ami3go/SLCAN-interface-hardware/Images/20240503_131544.jpg

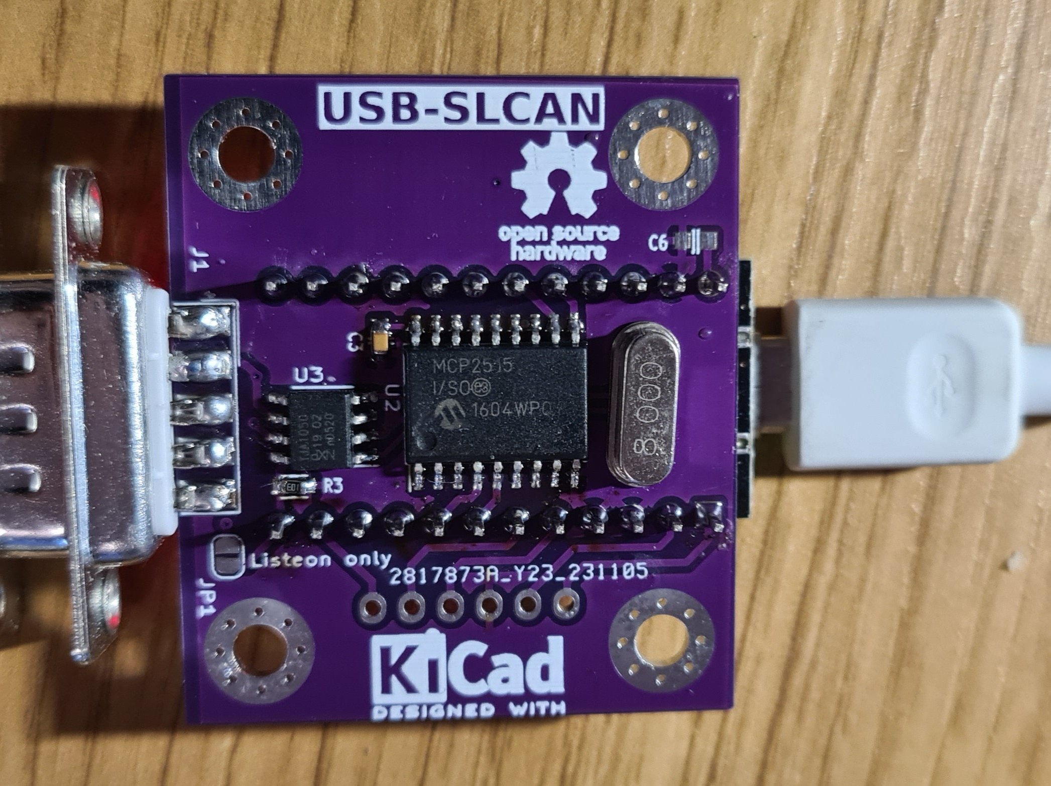
Images/20240503_131544.jpg
