ami3go/SLCAN-interface-hardware/Images/20240503_133706.jpg

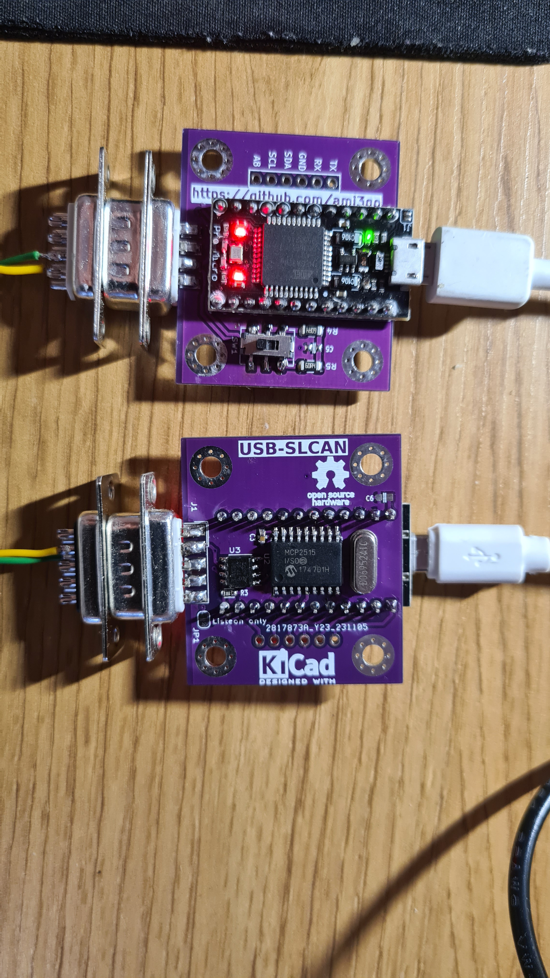
Images/20240503_133706.jpg
